DanyR2001/Laboratorio_di_making/Data/Umidità/GraphHumidity.png

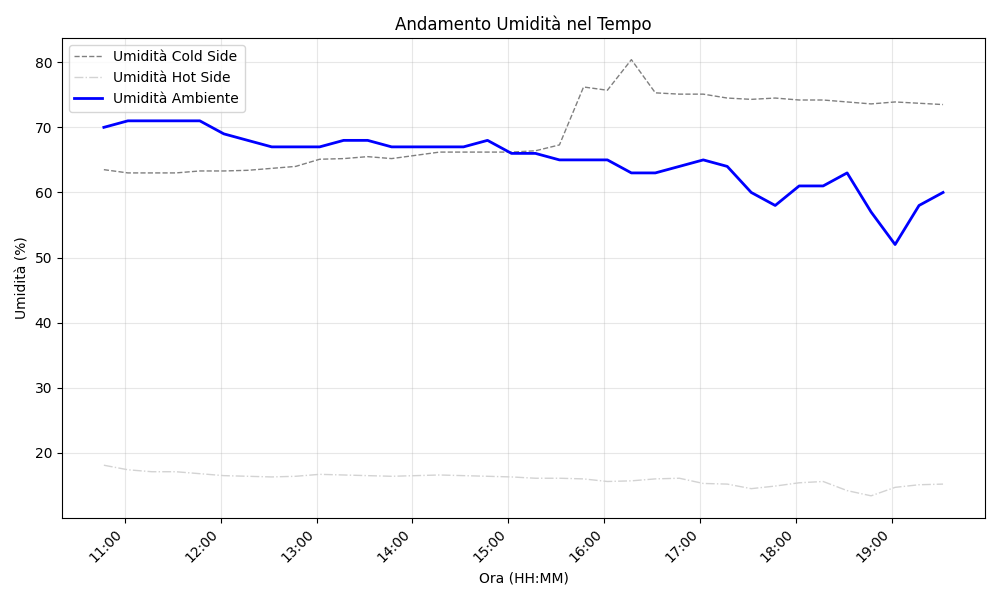
Data/Umidità/GraphHumidity.png
