DanyR2001/Laboratorio_di_making/Data/Rumore/Max velocity measurement.jpeg

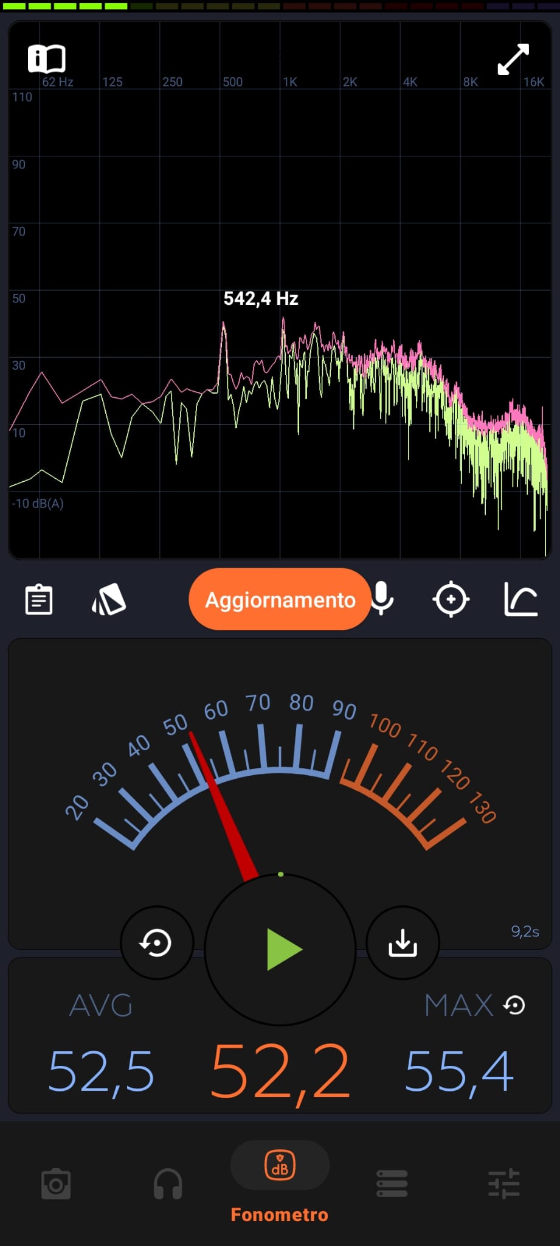
Data/Rumore/Max velocity measurement.jpeg
