DanyR2001/Laboratorio_di_making/Data/Rumore/Min velocity measurement.jpeg

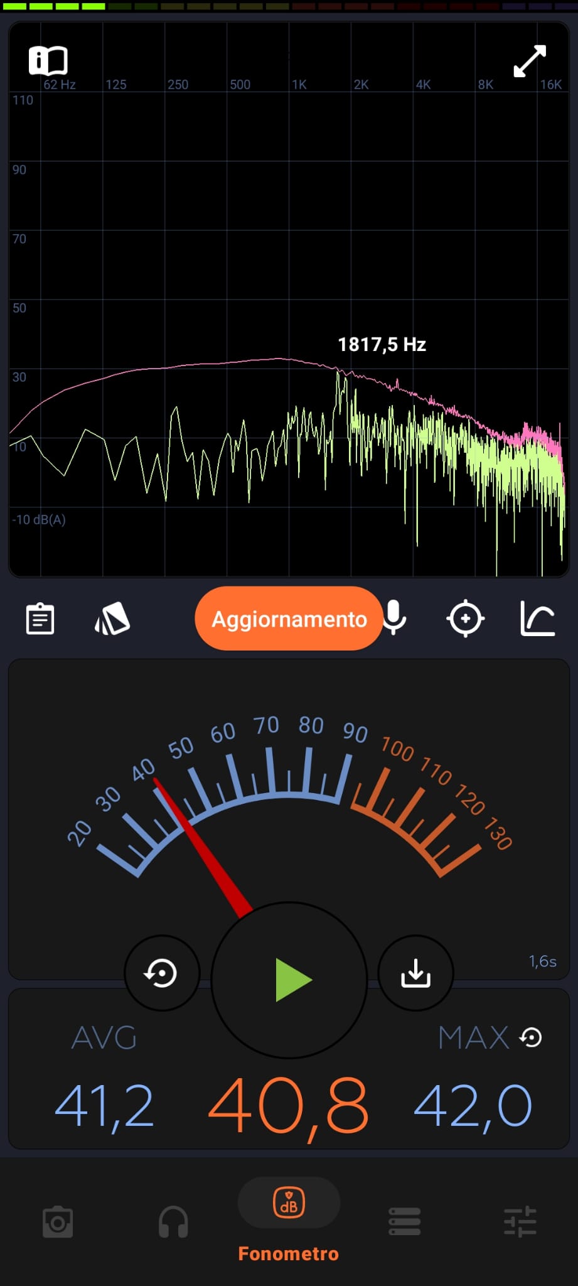
Data/Rumore/Min velocity measurement.jpeg
